slabua/keyboards/saru48wplus/cad/rev1/step/Saru48wPlus - Bottom Logo.step

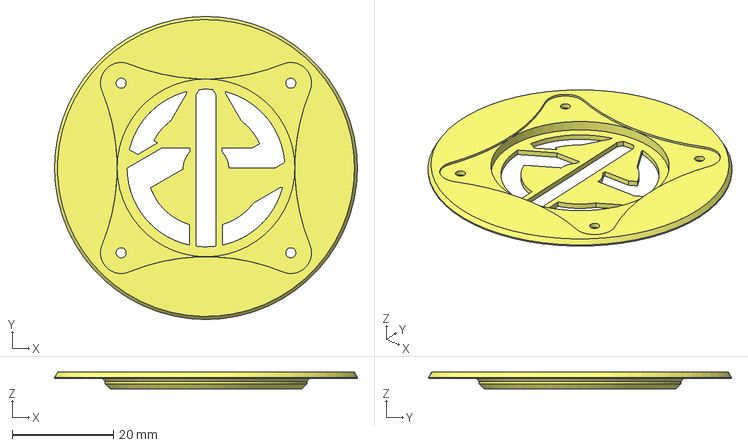
[picture p15: CAD file, 2024-01-11]
saru48wplus/cad/rev1/step/Saru48wPlus - Bottom Logo.step
60.0 x 60.0 x 3.30 mm
