slabua/keyboards/atreuslb50+/cad/rev1/AtreuSLB50-Foot.stl

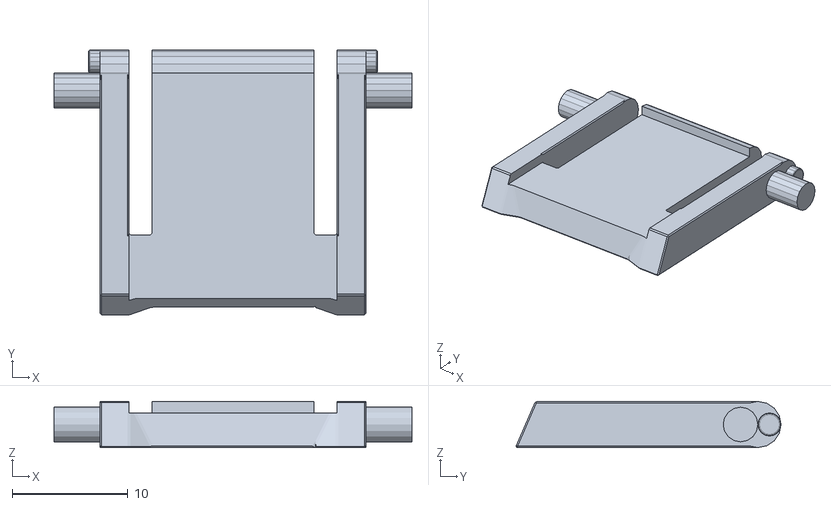
[picture p16: CAD file, 2022-11-13]
atreuslb50+/cad/rev1/AtreuSLB50-Foot.stl
31.0 x 23.0 x 4.00
