slabua/keyboards/saru48wplus/cad/rev1/step/Saru48wPlus - PlateR (CherryMX).step

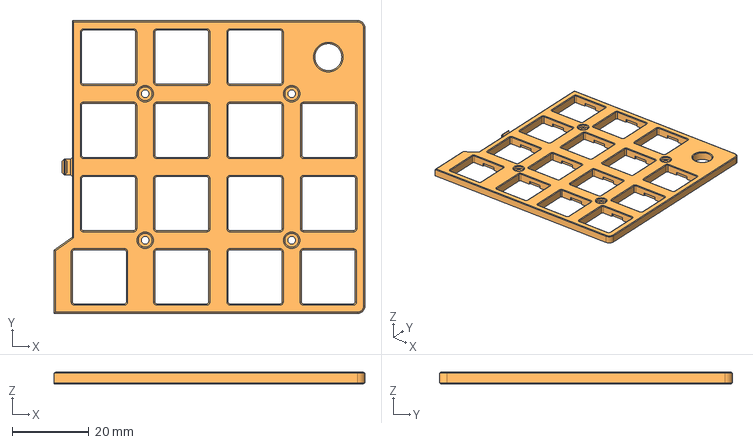
[picture p17: CAD file, 2024-01-11]
saru48wplus/cad/rev1/step/Saru48wPlus - PlateR (CherryMX).step
80.9 x 76.2 x 3.00 mm
