slabua/keyboards/atreuslb50+/cad/rev1/AtreuSLB50-PcbLeft.stl

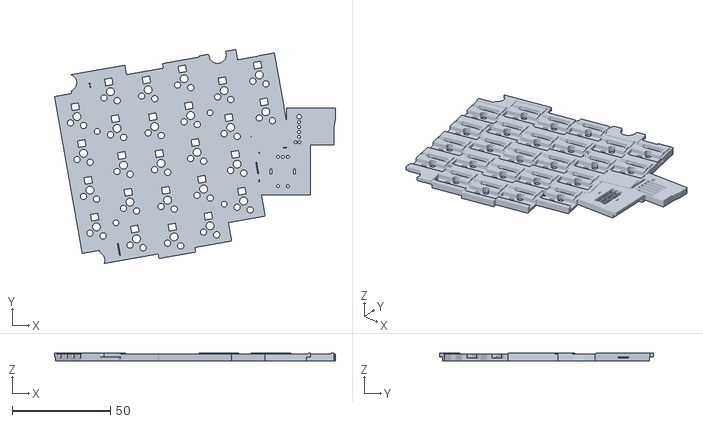
[picture p18: CAD file, 2022-11-13]
atreuslb50+/cad/rev1/AtreuSLB50-PcbLeft.stl
143.3 x 109.2 x 4.00
