slabua/keyboards/jeegva44ergozero/cad/rev1/step/JeegVa44ErgoZero-ErgoFoot.step

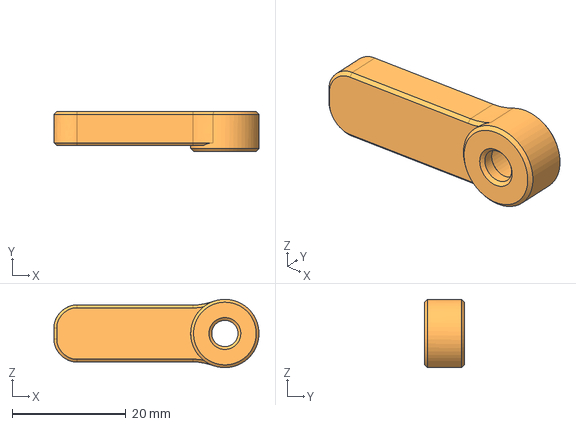
[picture p19: CAD file, 2023-02-19]
jeegva44ergozero/cad/rev1/step/JeegVa44ErgoZero-ErgoFoot.step
36.0 x 7.00 x 12.0 mm
