slabua/keyboards/saru48wplus/cad/rev1/step/Saru48wPlus - EC11 Knob.step

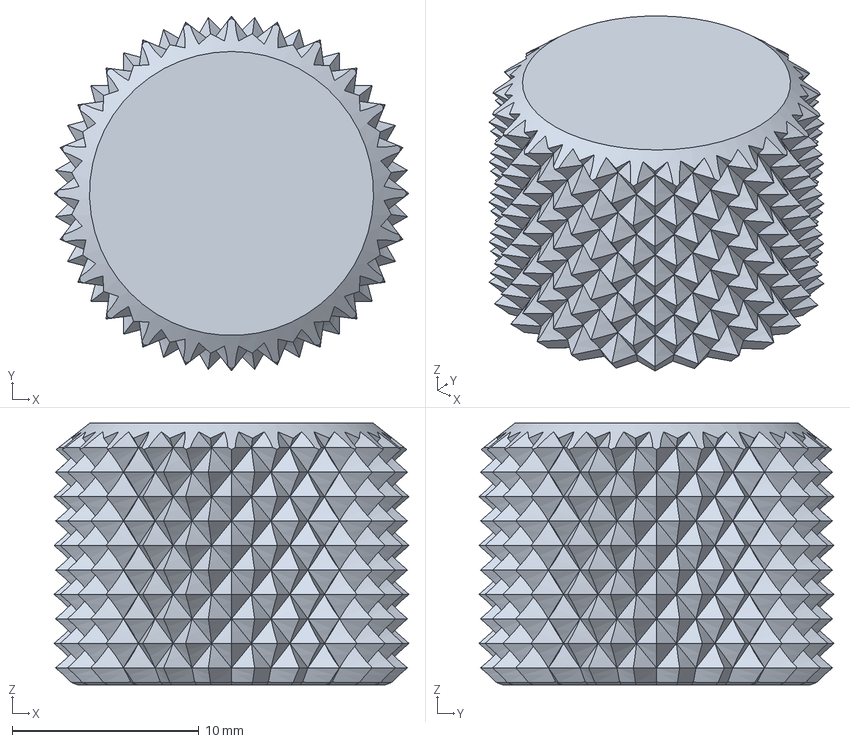
[picture p20: CAD file, 2024-01-11]
saru48wplus/cad/rev1/step/Saru48wPlus - EC11 Knob.step
19.0 x 19.0 x 14.0 mm
