slabua/keyboards/saru48wplus/cad/rev1/step/Saru48wPlus - ErgoFoot.step

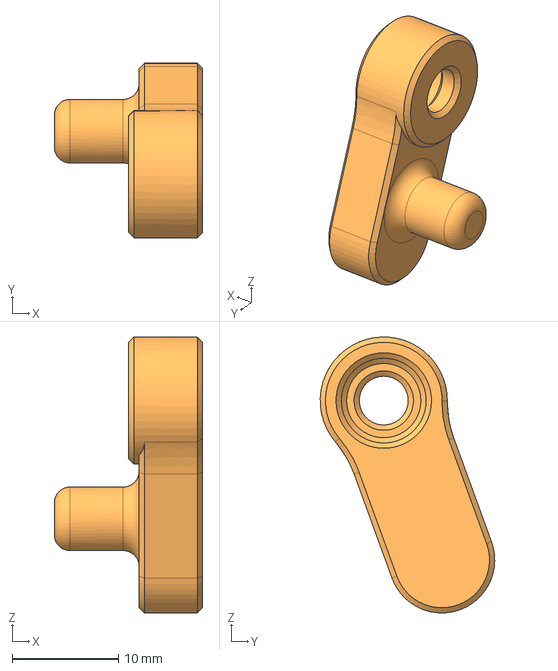
[picture p21: CAD file, 2024-01-11]
saru48wplus/cad/rev1/step/Saru48wPlus - ErgoFoot.step
14.0 x 16.5 x 26.0 mm
