slabua/keyboards/saru48wplus/cad/rev1/step/Saru48wPlus - CaseL.step

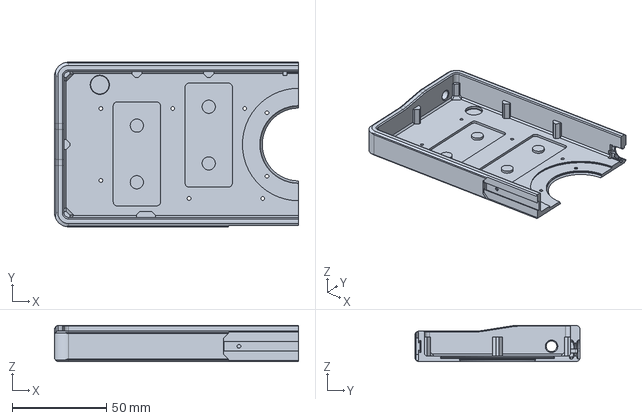
[picture p22: CAD file, 2024-01-11]
saru48wplus/cad/rev1/step/Saru48wPlus - CaseL.step
129.2 x 87.2 x 19.3 mm
