slabua/keyboards/saru48wplus/cad/rev1/step/Saru48wPlus - Bottom Logo filler.step

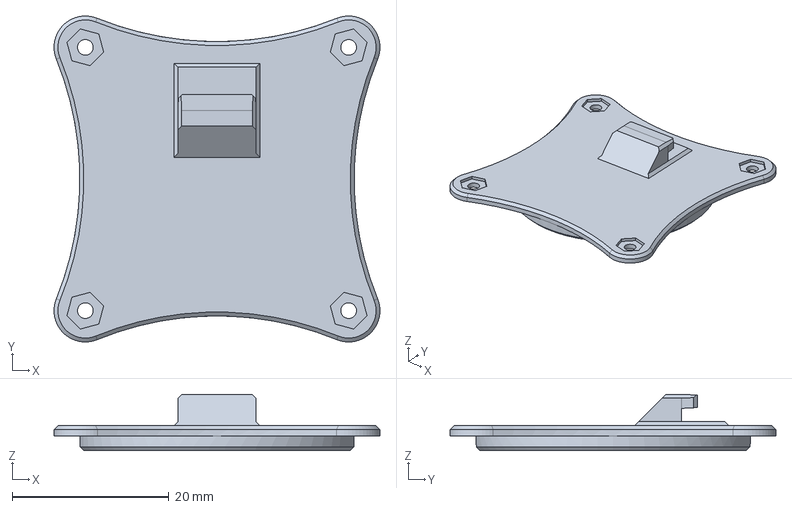
[picture p23: CAD file, 2024-01-11]
saru48wplus/cad/rev1/step/Saru48wPlus - Bottom Logo filler.step
41.6 x 41.6 x 7.20 mm
