slabua/keyboards/saru48wplus/cad/rev1/step/Saru48wPlus - PlateR (GateronLowProfile).step

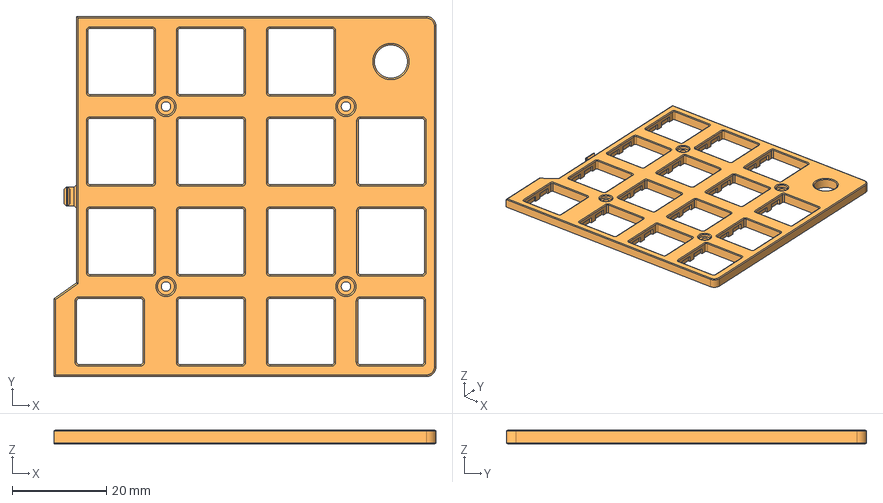
[picture p24: CAD file, 2024-01-11]
saru48wplus/cad/rev1/step/Saru48wPlus - PlateR (GateronLowProfile).step
80.9 x 76.2 x 3.00 mm
