slabua/keyboards/saru48wplus/cad/rev1/step/Saru48wPlus - Badge.step

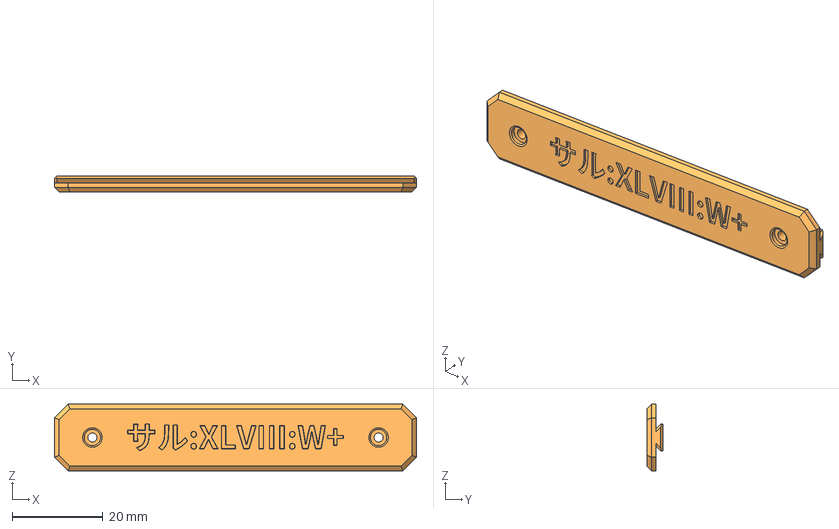
[picture p25: CAD file, 2024-01-11]
saru48wplus/cad/rev1/step/Saru48wPlus - Badge.step
80.0 x 3.50 x 14.7 mm
